techmiguel/stillpoint/docs/img/app_c_vs_python.png

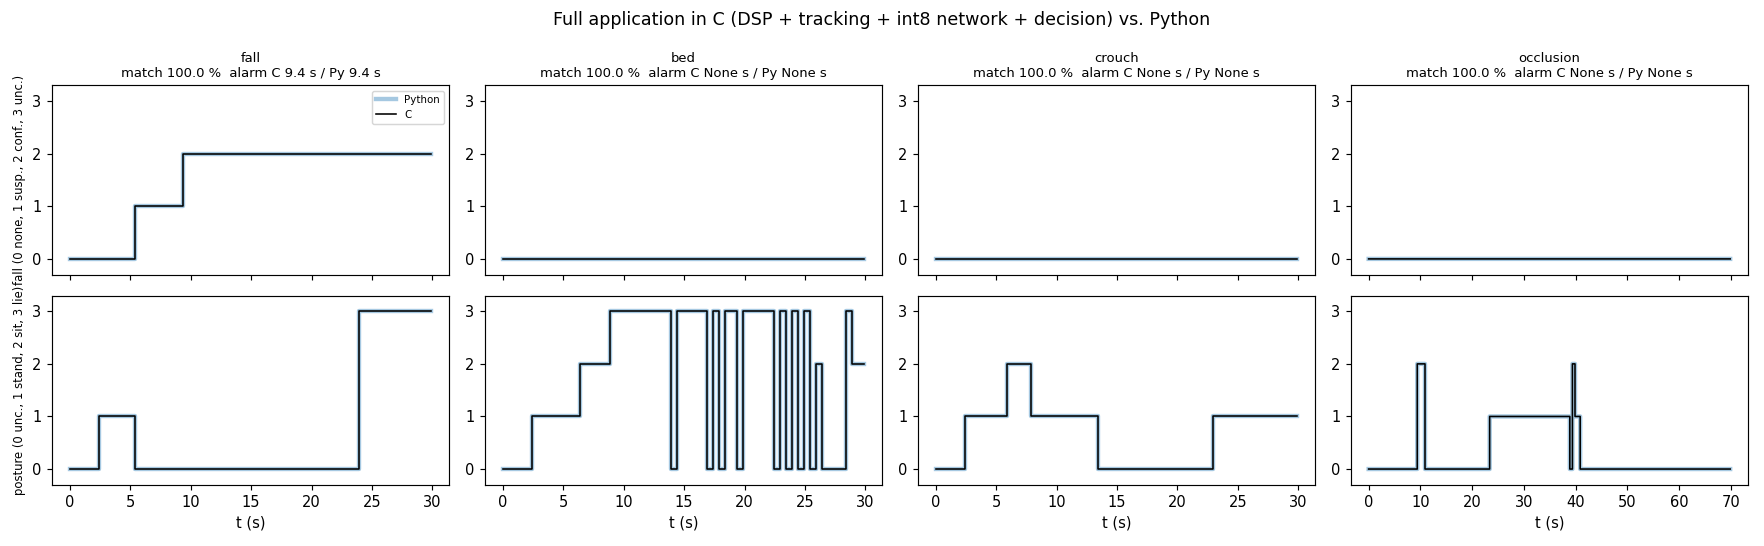
docs/img/app_c_vs_python.png
