techmiguel/stillpoint/docs/img/c_vs_python.png

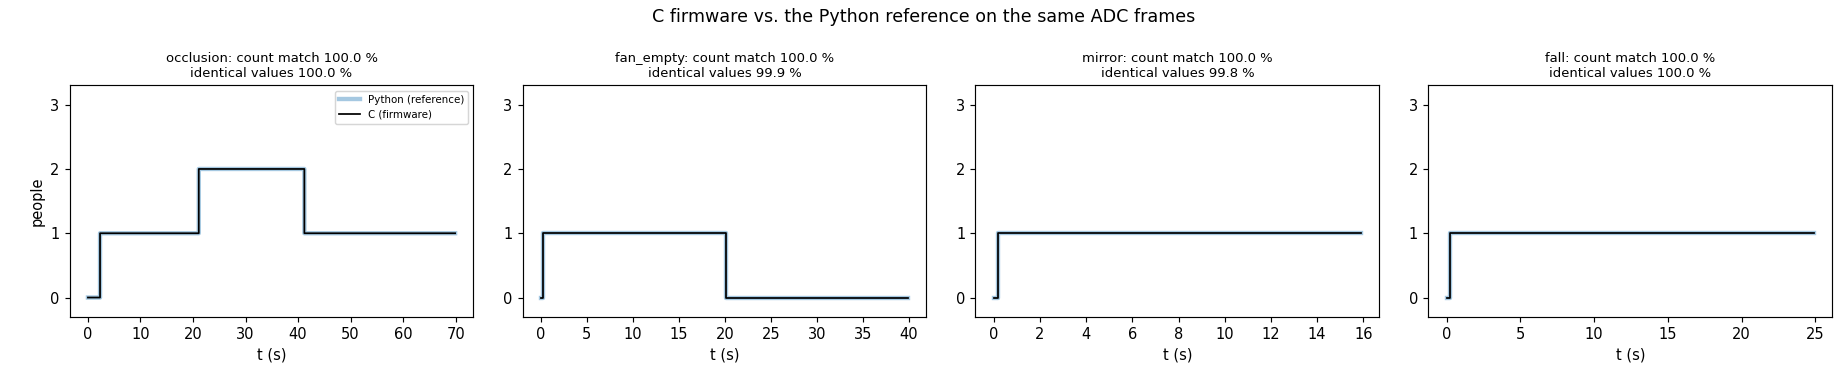
docs/img/c_vs_python.png
