techmiguel/stillpoint/docs/img/scenario_fall.png

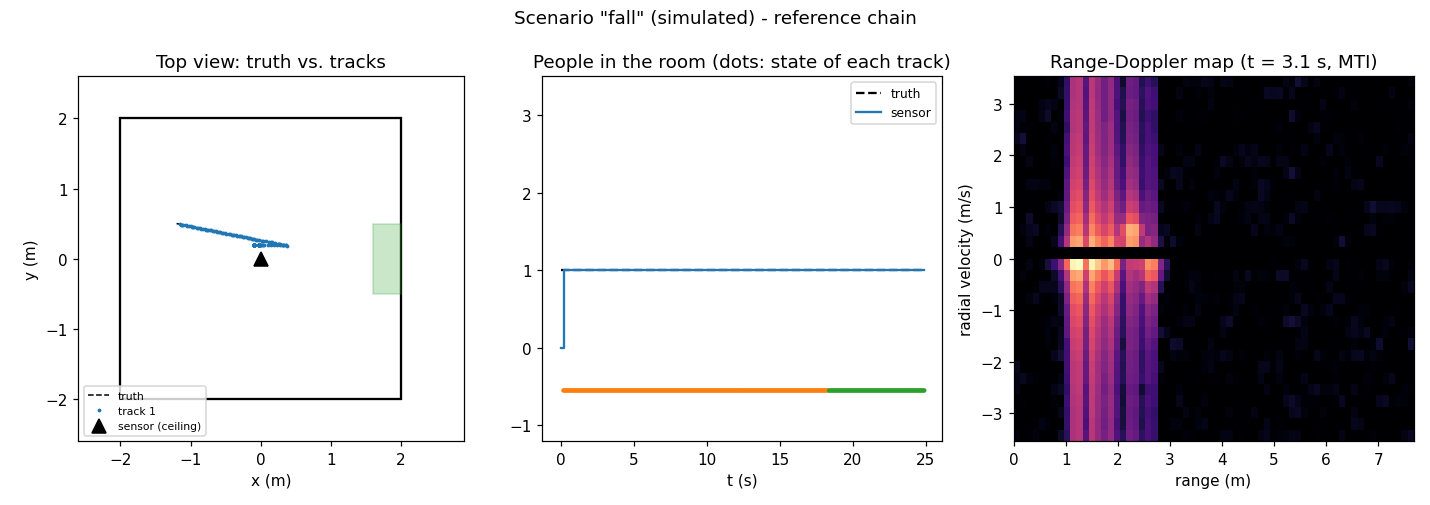
docs/img/scenario_fall.png
