techmiguel/stillpoint/docs/share/og.jpg

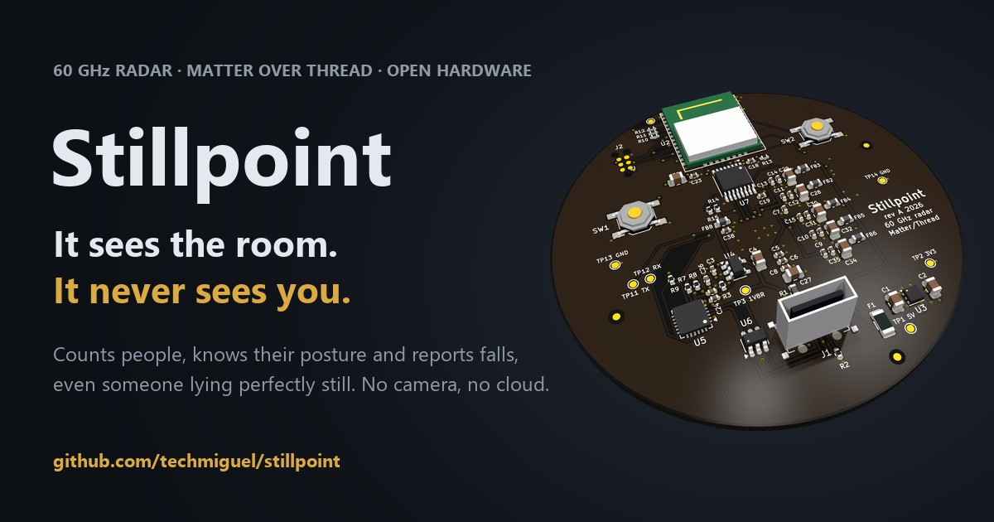
docs/share/og.jpg
