techmiguel/stillpoint/tools/pcb_build/placement.py

# ref: (x, y, rot, side). Board centre (100, 100), radius 30.
# Radar U1 on the bottom; its supply filters on the top right above it.
RX, RY = 100.0, 102.5          # radar centre
P = {
    # ---------------- bottom ----------------
    'U1': (RX, RY, 0, 'B'),
    'R4': (RX + 5.3, RY - 1.5, 180, 'B'),       # OSC series R, next to M2
    'Y1': (RX + 7.9, RY - 0.85, 180, 'B'),    # KC2016: OUT pad faces R4
    'C17': (RX + 9.9, RY - 0.85, 90, 'B'),     # 10n at Y1 VCC
    'C36': (RX + 11.0, RY - 0.85, 90, 'B'),    # 1u
    'FB7': (RX + 11.2, RY + 1.6, 0, 'B'),
    'U8': (110.8, 96.85, 180, 'B'),            # IRQ/DO translator, B side faces the radar lanes
    'C20': (114.6, 92.6, 0, 'B'),             # VCCA U8
    'C21': (108.0, 92.6, 0, 'B'),             # VCCB U8
    'R16': (115.0, 101.2, 0, 'B'),            # IRQ_3V3 pull-down
    'TP9': (117.2, 98.2, 0, 'B'),             # IRQ_3V3
    'TP5': (95.0, 90.0, 0, 'B'),              # SCLK
    'TP6': (97.4, 90.0, 0, 'B'),              # MOSI
    'TP7': (99.8, 90.0, 0, 'B'),              # MISO
    'TP8': (102.2, 90.0, 0, 'B'),             # CS
    'D1': (90.4, 79.0, 0, 'B'),               # RGB LED, shines through the radome
    'TP4': (88.0, 112.0, 0, 'B'),             # GND
    # ---------------- top: MCU ----------------
    'U2': (100.0, 78.5, 0, 'F'),
    'C23': (94.0, 88.0, 0, 'F'),
    'C22': (91.2, 88.0, 0, 'F'),
    'J2': (84.4, 81.0, 90, 'F'),
    'SW1': (83.4, 93.0, 0, 'F'),
    'SW2': (116.6, 86.0, 0, 'F'),
    'R10': (90.6, 76.7, 180, 'F'),
    'R11': (90.6, 75.7, 180, 'F'),
    'R12': (90.6, 74.7, 180, 'F'),
    'TP10': (91.0, 72.6, 0, 'F'),             # frame GPIO
    # ---------------- top: translator U7 ----------------
    'U7': (99.5, 91.4, -90, 'F'),
    'C18': (103.6, 88.3, 0, 'F'),             # VCCA U7
    'R13': (106.0, 88.3, 0, 'F'),             # OE pull-up
    'C19': (102.4, 95.9, 0, 'F'),            # VCCB U7
    'R14': (95.2, 95.6, 90, 'F'),             # CS_N pull-up (1V8_IO)
    'R15': (94.0, 95.6, 90, 'F'),             # DIO3 pull-up (1V8_IO)
    'FB8': (95.0, 98.6, 0, 'F'),
    'C38': (95.0, 100.2, 0, 'F'),
    # ---------------- top: radar supply filters ----------------
    # VDDD (FB3) / VDDA (FB2) / VDDRF-north: columns north-east of the via field
    'C13': (105.00, 93.68, -90, 'F'),
    'C14': (106.20, 93.68, -90, 'F'),
    'C29': (107.90, 94.15, -90, 'F'),
    'FB3': (110.60, 93.20, 180, 'F'),
    'C11': (105.40, 97.38, -90, 'F'),
    'C12': (106.60, 97.38, -90, 'F'),
    'C28': (108.30, 97.85, -90, 'F'),
    'FB2': (111.00, 96.90, 180, 'F'),
    'C7': (104.6, 99.73, -90, 'F'),
    'C16': (RX + 2.3, RY - 3.6, 90, 'B'),           # VAREF, at the ball
    # LF (FB4 from +3V3), PLL (FB5), VCO (FB6): east
    'C15': (106.10, 101.98, -90, 'F'),
    'C31': (107.30, 101.98, -90, 'F'),
    'C30': (109.00, 102.45, -90, 'F'),
    'FB4': (111.70, 101.50, 180, 'F'),
    'C10': (106.50, 105.58, -90, 'F'),
    'C33': (107.70, 105.58, -90, 'F'),
    'C32': (109.40, 106.05, -90, 'F'),
    'FB5': (112.10, 105.10, 180, 'F'),
    'C9': (106.50, 109.18, -90, 'F'),
    'C35': (107.70, 109.18, -90, 'F'),
    'C34': (109.40, 109.65, -90, 'F'),
    'FB6': (112.10, 108.70, 180, 'F'),
    # VDDRF south
    'C5': (100.48, 107.0, 0, 'F'),
    'C6': (100.48, 108.2, 0, 'F'),
    'C8': (100.48, 109.4, 0, 'F'),
    'C27': (100.95, 110.9, 0, 'F'),
    'FB1': (100.0, 113.4, 90, 'F'),
    # +1V8_RAD LDO
    'U4': (94.0, 107.0, 0, 'F'),
    'C3': (91.0, 106.0, 90, 'F'),
    'C4': (97.4, 107.0, 90, 'F'),
    'R3': (91.4, 108.8, 90, 'F'),
    'TP3': (94.0, 110.6, 0, 'F'),             # +1V8_RAD
    # ---------------- top: USB, 3.3 V ----------------
    'J1': (100.0, 119.0, 0, 'F'),
    'U6': (92.4, 118.0, 90, 'F'),
    'R1': (98.6, 114.6, 90, 'F'),
    'R2': (101.4, 123.4, -90, 'F'),
    'C39': (106.20, 117.40, 90, 'F'),
    'F1': (108.60, 121.80, 90, 'F'),
    'C1': (111.60, 119.80, 90, 'F'),
    'U3': (114.40, 119.80, 0, 'F'),
    'C2': (117.40, 119.80, 90, 'F'),
    'TP1': (111.60, 123.80, 0, 'F'),            # +5V
    'TP2': (119.6, 116.2, 0, 'F'),            # +3V3
    'U5': (86.0, 112.0, 180, 'F'),
    'C24': (89.7, 110.3, 0, 'F'),
    'C25': (89.7, 109.2, 0, 'F'),
    'C26': (89.7, 107.2, 90, 'F'),
    'R7': (86.95, 107.4, -90, 'F'),
    'R8': (88.15, 107.4, 90, 'F'),
    'R9': (85.2, 105.3, -90, 'F'),
    'TP11': (80.2, 104.0, 0, 'F'),            # VCOM TX
    'TP12': (82.6, 104.0, 0, 'F'),            # VCOM RX
    'TP13': (78.6, 100.0, 0, 'F'),            # GND
    'TP14': (121.4, 100.0, 0, 'F'),           # GND
}

FIDUCIALS = [
    (77.0, 108.0, 'F'), (123.0, 92.0, 'F'), (108.0, 126.5, 'F'),
    (78.0, 92.0, 'B'), (122.0, 108.0, 'B'), (92.0, 126.5, 'B'),
]
